Adesin-fr/piDrummer/ArduinoFirmware/src/piDrummerPins.h

#ifndef PIDRUMMERPINS_H_
#define PIDRUMMERPINS_H_

// Change this to reflect you number of installed inputs !
#define NB_ANALOG_CHANNELS 16

#define MUXER_AD0 10
#define MUXER_AD1 11
#define MUXER_AD2 12

#define encoderPinA 2
#define encoderPinB 3
#define EnterPushButton 4
#define EscapePushButton 6
#define PlayPushButton 7

#define POWER_BUTTON_PIN 5
#define POWER_LED_PIN 13
#define POWER_MOSFET_PIN 12

#define MSGTYPE_TRIGGER_VALUE 1
#define MSGTYPE_CONTROL_VALUE 2
#define MSGTYPE_AFTERTOUCH_VALUE 3
#define MSGTYPE_KEYPRESS_VALUE 4

#endif /* PIDRUMMERPINS_H_ */
